bcancinov/mdc-power-p3v3/sim/p3v3.asc

@1: fra; delay=1m fstart=5.53125K fend=1Meg oct=2 fcoarse=44.25K pp0=105.6m pp1=6.6m f0=5.53125K f1=88.5K tavgmin=50µ tsettle=11.2994µ
C1: cap; 1µF
C2: cap; 1µF
C3: cap; 22µ; Rser=40m Lser=1.7n
Coc1: cap; 47µF; x4; Rser=2.17m Lser=0.2n
Cth1: cap; 100n
Cthp1: cap; 27p
I1: current; PWL(0 0 2m 0 2.00001m 1)
R1: res; 10k
R2: res; 1.78k
R3: res; 100k
R4: res; '3.3/0.01'
R5: res; 0.5
Rfreq1: res; 47.5k
Riset1: res; 33.2k
Rth1: res; 1k
U1: LT8627SP
U2: XGL5030
V1: voltage; PULSE(0 3.3 0 1e-9 1e-9 0.25e-6 0.5e-6)
V2: voltage; 3.3
Vin2: voltage; 12V
Named nets: 0, SW, PGFB, SET, VOUT1, clk
LT8627SP - 18V, 16A Synchronous Step-Down Silent Switcher 3 with Ultra Low Noise
.tran 5m startup
* Adjust R1,R2,C1 as desired for start-up timing
Designer:
Date:
ProjectName:
.fra startup
